ZhuYanzhen1/MM32_CLion/testbench/riccati_solver/riccati_solver.c

#include "riccati_solver.h"
#include "stdio.h"
#include "math.h"

//  P = 96.7181   16.2375   -2.0601
//      16.2375   31.0814    8.2303
//      -2.0601    8.2303   11.3719

#define ITERATION_ACCURACY  0.01f

void solveRiccatiIteration(float A[3][3], float B[3][2], float Q[3][3], float R[2][2]) {
    float matrix_p_next[3][3] = {0}, matrix_p[3][3] = {{Q[0][0], Q[0][1], Q[0][2]},
                                                       {Q[1][0], Q[1][1], Q[1][2]},
                                                       {Q[2][0], Q[2][1], Q[2][2]}};
    for (unsigned int counter = 0; counter < 100000; ++counter) {
        float matrix_at_pn_a[3][3] =
            {{matrix_p[0][0], matrix_p[0][1], A[0][2] * matrix_p[0][0] + A[1][2] * matrix_p[0][1] + matrix_p[0][2]},
             {matrix_p[1][0], matrix_p[1][1], A[0][2] * matrix_p[1][0] + A[1][2] * matrix_p[1][1] + matrix_p[1][2]},
             {A[0][2] * matrix_p[0][0] + A[1][2] * matrix_p[1][0] + matrix_p[2][0],
              A[0][2] * matrix_p[0][1] + A[1][2] * matrix_p[1][1] + matrix_p[2][1],
              A[0][2] * matrix_p[0][2]
                  + A[1][2] * matrix_p[1][2]
                  + A[0][2] * (A[0][2] * matrix_p[0][0] + A[1][2] * matrix_p[1][0] + matrix_p[2][0])
                  + A[1][2] * (A[0][2] * matrix_p[0][1] + A[1][2] * matrix_p[1][1] + matrix_p[2][1]) + matrix_p[2][2]}};
        float
            matrix_at_pn_b[3][2] =
            {{B[0][0] * matrix_p[0][0] + B[1][0] * matrix_p[0][1] + B[2][0] * matrix_p[0][2], B[2][1] * matrix_p[0][2]},
             {B[0][0] * matrix_p[1][0] + B[1][0] * matrix_p[1][1] + B[2][0] * matrix_p[1][2], B[2][1] * matrix_p[1][2]},
             {B[0][0] * (A[0][2] * matrix_p[0][0] + A[1][2] * matrix_p[1][0] + matrix_p[2][0])
                  + B[1][0] * (A[0][2] * matrix_p[0][1] + A[1][2] * matrix_p[1][1] + matrix_p[2][1])
                  + B[2][0] * (A[0][2] * matrix_p[0][2] + A[1][2] * matrix_p[1][2] + matrix_p[2][2]),
              B[2][1] * (A[0][2] * matrix_p[0][2] + A[1][2] * matrix_p[1][2] + matrix_p[2][2])}};
        float matrix_r_bt_pn_b[2][2] =
            {{B[0][0] * (B[0][0] * matrix_p[0][0] + B[1][0] * matrix_p[1][0]
                + B[2][0] * matrix_p[2][0]) + B[1][0] * (B[0][0] * matrix_p[0][1] + B[1][0] * matrix_p[1][1]
                + B[2][0] * matrix_p[2][1])
                  + B[2][0] * (B[0][0] * matrix_p[0][2] + B[1][0] * matrix_p[1][2] + B[2][0] * matrix_p[2][2])
                  + R[0][0],
              B[2][1] * (B[0][0] * matrix_p[0][2] + B[1][0] * matrix_p[1][2] + B[2][0] * matrix_p[2][2])},
             {B[0][0] * B[2][1] * matrix_p[2][0]
                  + B[1][0] * B[2][1] * matrix_p[2][1] + B[2][0] * B[2][1] * matrix_p[2][2],
              B[2][1] * B[2][1] * matrix_p[2][2] + R[0][0]}};
        float
            matrix_bt_pn_a[2][3] =
            {{B[0][0] * matrix_p[0][0] + B[1][0] * matrix_p[1][0]
                  + B[2][0] * matrix_p[2][0],
              B[0][0] * matrix_p[0][1] + B[1][0] * matrix_p[1][1] + B[2][0] * matrix_p[2][1],
              B[0][0] * matrix_p[0][2]
                  + B[1][0] * matrix_p[1][2]
                  + A[0][2] * (B[0][0] * matrix_p[0][0]
                      + B[1][0] * matrix_p[1][0]
                      + B[2][0] * matrix_p[2][0])
                  + A[1][2] * (B[0][0] * matrix_p[0][1]
                      + B[1][0] * matrix_p[1][1] + B[2][0] * matrix_p[2][1]) + B[2][0] * matrix_p[2][2]},
             {B[2][1] * matrix_p[2][0],
              B[2][1] * matrix_p[2][1],
              A[0][2] * B[2][1] * matrix_p[2][0] + A[1][2] * B[2][1] * matrix_p[2][1] + B[2][1] * matrix_p[2][2]}};
        float matrix_inv_r_bt_pn_b[2][2] =
            {{matrix_r_bt_pn_b[1][1]
                  / (-matrix_r_bt_pn_b[0][1] * matrix_r_bt_pn_b[1][0]
                      + matrix_r_bt_pn_b[0][0] * matrix_r_bt_pn_b[1][1]), -(matrix_r_bt_pn_b[0][1]
                / (-matrix_r_bt_pn_b[0][1] * matrix_r_bt_pn_b[1][0]
                    + matrix_r_bt_pn_b[0][0] * matrix_r_bt_pn_b[1][1]))},
             {-(matrix_r_bt_pn_b[1][0]
                 / (-matrix_r_bt_pn_b[0][1] * matrix_r_bt_pn_b[1][0]
                     + matrix_r_bt_pn_b[0][0] * matrix_r_bt_pn_b[1][1])),
              matrix_r_bt_pn_b[0][0] / (-matrix_r_bt_pn_b[0][1] * matrix_r_bt_pn_b[1][0]
                  + matrix_r_bt_pn_b[0][0] * matrix_r_bt_pn_b[1][1])}};
        float another_matrix[3][3] =
            {{(matrix_at_pn_b[0][0] * matrix_inv_r_bt_pn_b[0][0]
                + matrix_at_pn_b[0][1] * matrix_inv_r_bt_pn_b[1][0]) * matrix_bt_pn_a[0][0]
                  + (matrix_at_pn_b[0][0] * matrix_inv_r_bt_pn_b[0][1]
                      + matrix_at_pn_b[0][1] * matrix_inv_r_bt_pn_b[1][1]) * matrix_bt_pn_a[1][0],
              (matrix_at_pn_b[0][0] * matrix_inv_r_bt_pn_b[0][0] +
                  matrix_at_pn_b[0][1] * matrix_inv_r_bt_pn_b[1][0]) * matrix_bt_pn_a[0][1]
                  + (matrix_at_pn_b[0][0] * matrix_inv_r_bt_pn_b[0][1]
                      + matrix_at_pn_b[0][1] * matrix_inv_r_bt_pn_b[1][1]) * matrix_bt_pn_a[1][1],
              (matrix_at_pn_b[0][0] * matrix_inv_r_bt_pn_b[0][0] +
                  matrix_at_pn_b[0][1] * matrix_inv_r_bt_pn_b[1][0]) * matrix_bt_pn_a[0][2]
                  + (matrix_at_pn_b[0][0] * matrix_inv_r_bt_pn_b[0][1]
                      + matrix_at_pn_b[0][1] * matrix_inv_r_bt_pn_b[1][1]) * matrix_bt_pn_a[1][2]},
             {(matrix_at_pn_b[1][0] * matrix_inv_r_bt_pn_b[0][0] +
                 matrix_at_pn_b[1][1] * matrix_inv_r_bt_pn_b[1][0]) * matrix_bt_pn_a[0][0]
                  + (matrix_at_pn_b[1][0] * matrix_inv_r_bt_pn_b[0][1]
                      + matrix_at_pn_b[1][1] * matrix_inv_r_bt_pn_b[1][1]) * matrix_bt_pn_a[1][0],
              (matrix_at_pn_b[1][0] * matrix_inv_r_bt_pn_b[0][0] +
                  matrix_at_pn_b[1][1] * matrix_inv_r_bt_pn_b[1][0]) * matrix_bt_pn_a[0][1]
                  + (matrix_at_pn_b[1][0] * matrix_inv_r_bt_pn_b[0][1]
                      + matrix_at_pn_b[1][1] * matrix_inv_r_bt_pn_b[1][1]) * matrix_bt_pn_a[1][1],
              (matrix_at_pn_b[1][0] * matrix_inv_r_bt_pn_b[0][0] +
                  matrix_at_pn_b[1][1] * matrix_inv_r_bt_pn_b[1][0]) * matrix_bt_pn_a[0][2]
                  + (matrix_at_pn_b[1][0] * matrix_inv_r_bt_pn_b[0][1]
                      + matrix_at_pn_b[1][1] * matrix_inv_r_bt_pn_b[1][1]) * matrix_bt_pn_a[1][2]},
             {(matrix_at_pn_b[2][0] * matrix_inv_r_bt_pn_b[0][0] +
                 matrix_at_pn_b[2][1] * matrix_inv_r_bt_pn_b[1][0]) * matrix_bt_pn_a[0][0]
                  + (matrix_at_pn_b[2][0] * matrix_inv_r_bt_pn_b[0][1]
                      + matrix_at_pn_b[2][1] * matrix_inv_r_bt_pn_b[1][1]) * matrix_bt_pn_a[1][0],
              (matrix_at_pn_b[2][0] * matrix_inv_r_bt_pn_b[0][0] +
                  matrix_at_pn_b[2][1] * matrix_inv_r_bt_pn_b[1][0]) * matrix_bt_pn_a[0][1]
                  + (matrix_at_pn_b[2][0] * matrix_inv_r_bt_pn_b[0][1]
                      + matrix_at_pn_b[2][1] * matrix_inv_r_bt_pn_b[1][1]) * matrix_bt_pn_a[1][1],
              (matrix_at_pn_b[2][0] * matrix_inv_r_bt_pn_b[0][0] +
                  matrix_at_pn_b[2][1] * matrix_inv_r_bt_pn_b[1][0]) * matrix_bt_pn_a[0][2]
                  + (matrix_at_pn_b[2][0] * matrix_inv_r_bt_pn_b[0][1]
                      + matrix_at_pn_b[2][1] * matrix_inv_r_bt_pn_b[1][1]) * matrix_bt_pn_a[1][2]}};
        matrix_p_next[0][0] = matrix_at_pn_a[0][0] - another_matrix[0][0] + Q[0][0];
        matrix_p_next[0][1] = matrix_at_pn_a[0][1] - another_matrix[0][1];
        matrix_p_next[0][2] = matrix_at_pn_a[0][2] - another_matrix[0][2];
        matrix_p_next[1][0] = matrix_at_pn_a[1][0] - another_matrix[1][0];
        matrix_p_next[1][1] = matrix_at_pn_a[1][1] - another_matrix[1][1] + Q[0][0];
        matrix_p_next[1][2] = matrix_at_pn_a[1][2] - another_matrix[1][2];
        matrix_p_next[2][0] = matrix_at_pn_a[2][0] - another_matrix[2][0];
        matrix_p_next[2][1] = matrix_at_pn_a[2][1] - another_matrix[2][1];
        matrix_p_next[2][2] = matrix_at_pn_a[2][2] - another_matrix[2][2] + Q[0][0];

        float p_next_max_coefficient = fabsf(matrix_p_next[0][0]);
        for (unsigned char counter1 = 0; counter1 < 3; ++counter1)
            for (unsigned char counter2 = 0; counter2 < 3; ++counter2)
                if (p_next_max_coefficient < fabsf(matrix_p_next[counter1][counter2]))
                    p_next_max_coefficient = fabsf(matrix_p_next[counter1][counter2]);

        float p_max_coefficient = fabsf(matrix_p[0][0]);
        for (unsigned char counter1 = 0; counter1 < 3; ++counter1)
            for (unsigned char counter2 = 0; counter2 < 3; ++counter2)
                if (p_max_coefficient < fabsf(matrix_p[counter1][counter2]))
                    p_max_coefficient = fabsf(matrix_p[counter1][counter2]);

        if (fabsf(p_max_coefficient - p_next_max_coefficient) < ITERATION_ACCURACY) {
            printf("\r\niteration counter:%d\r\n", counter);
            break;
        }

        for (unsigned char counter1 = 0; counter1 < 3; ++counter1)
            for (unsigned char counter2 = 0; counter2 < 3; ++counter2)
                matrix_p[counter1][counter2] = matrix_p_next[counter1][counter2];
    }

    printf("------------Matrix P------------\r\n");
    for (int counter1 = 0; counter1 < 3; ++counter1) {
        for (int counter2 = 0; counter2 < 3; ++counter2)
            printf("%f   ", matrix_p[counter1][counter2]);
        printf("\r\n");
    }
}
