ZhuYanzhen1/MM32_CLion/program/math/path.c

/**************************************************************************/ /**
    \file     path.c
    \brief    Contains track points
    \author   ZGL
    \version  V1.6.1
    \date     24. July 2022
 ******************************************************************************/

#include "path.h"

float test_point[][4] = {
    {4302.6909513f, 39718.6588341f, 3.0595232f, 0.0002376f},
    {4302.2433562f, 39718.6956507f, 3.0787849f, 0.0009164f},
    {4301.7594206f, 39718.7260856f, 3.0838215f, 0.0003204f},
    {4301.2719785f, 39718.7542770f, 3.0873939f, 0.0001274f},
    {4300.7692807f, 39718.7815493f, 3.0928840f, 0.0002585f},
    {4300.2493526f, 39718.8068944f, 3.0954987f, 0.0001789f},
    {4299.7288173f, 39718.8309050f, 3.1034684f, 0.0004699f},
    {4299.1937356f, 39718.8513145f, 3.1115700f, 0.0005022f},
    {4298.6453620f, 39718.8677830f, 3.1129434f, 0.0001222f},
    {4298.1037258f, 39718.8833047f, 3.1148885f, 0.0001497f},
    {4297.5657533f, 39718.8976742f, 3.0111398f, 0.0072814f},
    {4297.0174779f, 39718.9696068f, 2.9971062f, 0.0009579f},
    {4296.4701301f, 39719.0492461f, 3.0061274f, 0.0004470f},
    {4295.9127171f, 39719.1252215f, 3.0175074f, 0.0005869f},
    {4295.3428454f, 39719.1962994f, 3.0307719f, 0.0009550f},
    {4294.7751609f, 39719.2594694f, 3.0416822f, 0.0006085f},
    {4294.1960448f, 39719.3175225f, 3.0546844f, 0.0008802f},
    {4293.6147403f, 39719.3681702f, 3.0611917f, 0.0002613f},
    {4293.0142663f, 39719.4165532f, 3.0723577f, 0.0008467f},
    {4292.4209396f, 39719.4576979f, 3.0783939f, 0.0003856f},
    {4291.8231457f, 39719.4955281f, 3.0847742f, 0.0003889f},
    {4291.2175311f, 39719.5299753f, 3.0919340f, 0.0005399f},
    {4290.6178780f, 39719.5597778f, 3.0953611f, 0.0001098f},
    {4289.9948902f, 39719.5886000f, 3.0998538f, 0.0004809f},
    {4289.4025012f, 39719.6133400f, 3.1031333f, 0.0001459f},
    {4288.7926511f, 39719.6368060f, 3.1079789f, 0.0003114f},
    {4288.1764860f, 39719.6575254f, 3.1112980f, 0.0002353f},
    {4287.5611374f, 39719.6761729f, 3.1130251f, 0.0001703f},
    {4286.9598236f, 39719.6933556f, 3.1154136f, 0.0002034f},
    {4286.3692413f, 39719.7088200f, 3.1162437f, 0.0000527f},
    {4285.7769171f, 39719.7238380f, 3.1182080f, 0.0001295f},
    {4285.1819254f, 39719.7377542f, 3.1203890f, 0.0001648f},
    {4284.5913329f, 39719.7502788f, 3.1226512f, 0.0001473f},
    {4283.9962996f, 39719.7615509f, 3.1255383f, 0.0002317f},
    {4283.4142696f, 39719.7708958f, 3.1252645f, 0.0000316f},
    {4282.8257427f, 39719.7805062f, 3.1284448f, 0.0002064f},
    {4282.2287684f, 39719.7883556f, 3.1298461f, 0.0000913f},
    {4281.6273916f, 39719.7954201f, 3.1329040f, 0.0002089f},
    {4281.0222524f, 39719.8006780f, 3.1305565f, 0.0001601f},
    {4280.4213272f, 39719.8073102f, 3.1324097f, 0.0001227f},
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
};
