ZhuYanzhen1/MM32_CLion/program/math/data_conversion.c

/**************************************************************************/ /**
    \file       data_conversion.c
    \brief      Coordinate system transformation
                Data Transformation
    \author     ZGL
    \version    V1.6.1
    \date       24. July 2022
******************************************************************************/

#include "data_conversion.h"
#include "qfplib.h"
#include "gps_parser.h"
#include "sensor_decode.h"
#include "fast_math.h"
#include "kalman.h"

extern kalman_data_t kalman_data;

/*! \brief Status information in the neu coordinates */
neu_infomation neu = {0};

/*!
    \brief      Get the distance based on the latitude and longitude of the starting point
                and the latitude and longitude of the current state
    \param[in]  lat_1(°):Starting latitude
    \param[in]  lon_1(°):Starting longitude
    \param[in]  lat_2(°):Latitude of Present State
    \param[in]  lon_2(°):longitude of Present State
    \retval     Distance between two points on the earth
    \note       When we keep the longitude the same, we can calculate the distance to the north
                When we keep the latitude the same, we can calculate the distance to the east
*/
float get_distance(float lat_2, float lon_2, float lat_1, float lon_1) {
    float temp =
        my_pow(qfp_fsin(GEO_ANGLE((lat_1 - lat_2) * 0.5f)), 2) +
            qfp_fcos(GEO_ANGLE(lat_1)) * qfp_fcos(GEO_ANGLE(lat_2))
                * my_pow(qfp_fsin(GEO_ANGLE((lon_1 - lon_2) * 0.5f)), 2);
    float distance = 2 * EARTH_RADIUS * my_asin(qfp_fsqrt(temp));
    return distance;
}

/*!
    \brief      Convert latitude to displacement in ENU coordinate system
    \param[in]  latitude(°)
    \retval     Converted data
*/
float get_distance_m_lat(float lat) {
    float distance = GEO_ANGLE(lat);
    return EARTH_RADIUS * distance;
}

/*!
    \brief      Convert longitude to displacement in ENU coordinate system
    \param[in]  longitude(°)
    \retval     Converted data
*/
float get_distance_m_lon(float lon) {
    float distance = GEO_ANGLE(lon);
    return EARTH_RADIUS * distance;
}

/*!
    \brief  Converting GPS-derived latitude,
            longitude, velocity and acceleration into the international system of units
*/
void sensor_unit_conversion() {
    if (small_packets_sum.num == 0)
        small_packets_sum.ay = 0;
    else
        small_packets_sum.ay /= (float) small_packets_sum.num;
    neu.acceleration = MG_TO_M_S_2(small_packets_sum.ay * FACTOR_ALLC_Y);   // 车头前进的方向时y的正方向
    small_packets_sum.num = 0;
    small_packets_sum.ay = 0;

    float temp_v = (float) gps_rmc.speed_to_ground_section;
    int v_decimal = num_times_nth_power_of_10(1, gps_rmc.decimal_places_speed);
    neu.v = KNOT_TO_M_S(temp_v / v_decimal);
}

/*
    \brief  The velocity obtained after Kalman filtering
            becomes the velocity in the northeast sky coordinate system
*/
void coordinate_system_transformation_kalman_v(float delta) {
    float temp_delta = GEO_ANGLE(delta);
    neu.north_v = kalman_data.v * qfp_fcos(temp_delta);
    neu.east_v = kalman_data.v * qfp_fsin(temp_delta);
}
