ZhuYanzhen1/MM32_CLion/program/math/path.h

/**************************************************************************/ /**
    \file     path.h
    \brief    Contains macros related to track points
    \author   ZGL
    \version  V1.6.1
    \date     24. July 2022
 ******************************************************************************/

#ifndef MM32F3277_MATH_TEST_H_
#define MM32F3277_MATH_TEST_H_

/*! \brief Number of track points */
#define INDEX_NUM   700

extern float test_point[][4];

#endif // MM32F3277_MATH_TEST_H_
