ZhuYanzhen1/MM32_CLion/program/hardware/gpio.c

/**************************************************************************/ /**
    \file       gpio.c
    \brief      GPIO function Source File
    \author     LaoZhu
    \version    V1.6.1
    \date       24. July 2022
******************************************************************************/

#include "gpio.h"
#ifdef IS_CONTROL_MCU
#include "../ctrl_mcu/config.h"
#include "../ctrl_mcu/pin.h"
#else
#include "../proc_mcu/config.h"
#include "../proc_mcu/pin.h"
#endif  // IS_CONTROL_MCU
#include "hal_conf.h"
#include "mm32_device.h"

#ifdef IS_CONTROL_MCU

void tim3_pwm_gpio_config(void) {
    GPIO_InitTypeDef GPIO_InitStructure;
    RCC_AHBPeriphClockCmd(RCC_AHBPeriph_GPIOB, ENABLE);
    GPIO_InitStructure.GPIO_Pin = GPIO_Pin_4;
    GPIO_InitStructure.GPIO_Mode = GPIO_Mode_Out_PP;
    GPIO_InitStructure.GPIO_Speed = GPIO_Speed_50MHz;
    GPIO_Init(GPIOB, &GPIO_InitStructure);
    GPIO_ResetBits(GPIOB, GPIO_Pin_4);
}

#endif
#ifdef IS_PROCESS_MCU
void lcd_gpio_config(void) {
    GPIO_InitTypeDef GPIO_InitStruct;
    RCC_AHBPeriphClockCmd(RCC_AHBENR_GPIOE, ENABLE);

    GPIO_StructInit(&GPIO_InitStruct);
    GPIO_InitStruct.GPIO_Pin = LCD_A0_PIN;
    GPIO_InitStruct.GPIO_Speed = GPIO_Speed_50MHz;
    GPIO_InitStruct.GPIO_Mode = GPIO_Mode_Out_PP;
    GPIO_Init(LCD_A0_PORT, &GPIO_InitStruct);

    GPIO_StructInit(&GPIO_InitStruct);
    GPIO_InitStruct.GPIO_Pin = LCD_RES_PIN;
    GPIO_InitStruct.GPIO_Speed = GPIO_Speed_50MHz;
    GPIO_InitStruct.GPIO_Mode = GPIO_Mode_Out_PP;
    GPIO_Init(LCD_RES_PORT, &GPIO_InitStruct);
}

void xpt2046_gpio_config(void) {
    GPIO_InitTypeDef GPIO_InitStruct;
    NVIC_InitTypeDef NVIC_InitStruct;
    EXTI_InitTypeDef EXTI_InitStruct;

    RCC_APB2PeriphClockCmd(RCC_APB2ENR_SYSCFG, ENABLE);
    RCC_AHBPeriphClockCmd(RCC_AHBENR_GPIOE, ENABLE);

    GPIO_StructInit(&GPIO_InitStruct);
    GPIO_InitStruct.GPIO_Pin = TOUCH_CS_PIN;
    GPIO_InitStruct.GPIO_Speed = GPIO_Speed_50MHz;
    GPIO_InitStruct.GPIO_Mode = GPIO_Mode_Out_PP;
    GPIO_Init(TOUCH_CS_PORT, &GPIO_InitStruct);

    GPIO_StructInit(&GPIO_InitStruct);
    GPIO_InitStruct.GPIO_Pin = TOUCH_PEN_PIN;
    GPIO_InitStruct.GPIO_Speed = GPIO_Speed_50MHz;
    GPIO_InitStruct.GPIO_Mode = GPIO_Mode_IPU;
    GPIO_Init(TOUCH_PEN_PORT, &GPIO_InitStruct);

    SYSCFG_EXTILineConfig(EXTI_PortSourceGPIOE, EXTI_PinSource4);
    EXTI_InitStruct.EXTI_Line = EXTI_Line4;
    EXTI_InitStruct.EXTI_Mode = EXTI_Mode_Interrupt;
    EXTI_InitStruct.EXTI_Trigger = EXTI_Trigger_Falling;
    EXTI_InitStruct.EXTI_LineCmd = ENABLE;
    EXTI_Init(&EXTI_InitStruct);

    NVIC_InitStruct.NVIC_IRQChannel = EXTI4_IRQn;
    NVIC_InitStruct.NVIC_IRQChannelPreemptionPriority = EXTI4_PRIORITY;
    NVIC_InitStruct.NVIC_IRQChannelSubPriority = 0;
    NVIC_InitStruct.NVIC_IRQChannelCmd = ENABLE;
    NVIC_Init(&NVIC_InitStruct);

    GPIO_SetBits(TOUCH_PEN_PORT, TOUCH_PEN_PIN);
    GPIO_SetBits(TOUCH_CS_PORT, TOUCH_CS_PIN);
}
#endif  // IS_PROCESS_MCU
