ZhuYanzhen1/MM32_CLion/program/hardware/timer.h

/**************************************************************************/ /**
    \file     timer.h
    \brief    Tim function Header File
    \author   Lao·Zhu
    \version  V1.6.1
    \date     24. July 2022
******************************************************************************/

#ifndef MM32F3277_HARDWARE_TIMER_H_
#define MM32F3277_HARDWARE_TIMER_H_

void timer2_config();
void timer3_config(void);

#endif // MM32F3277_HARDWARE_TIMER_H_
