ZhuYanzhen1/MM32_CLion/program/math/kalman.h

/**************************************************************************/ /**
    \file       kalman.h
    \brief      Kalman Fusion Header File
    \author     ZGL
    \version    V1.6.1
    \date       24. July 2022
******************************************************************************/

#ifndef MM32F3277_MATH_KALMAN_H_
#define MM32F3277_MATH_KALMAN_H_

#define V_Q_POS     0.2f
#define DIS_Q_POS   0.8f

/*! \brief The data after performing Kalman fusion */
typedef struct {
    float v;
    float distance_north;
    float distance_east;
} kalman_data_t;

typedef struct {
    float q_pos; // Process noise variance for the position
    float q_vel; // Process noise variance for the velocity
    float r_pos; // Measurement noise variance - this is actually the variance of the measurement noise
    float r_old_pos;

    float pos;   // The pos calculated by the Kalman filter - part of the 2x1 state vector
    float vel;   // The gyro velocity calculated by the Kalman filter - part of the 2x1 state vector
    float bias;  // The bias of velocity

    float P[2][2]; // Error covariance 2x2 matrix
    unsigned char gps_valid_flag;
} kalman_filter_t;

void kalman_config_angle(kalman_filter_t *kalman, float pos_0);
void kalman_config_v(kalman_filter_t *kalman);
void kalman_config_distance(kalman_filter_t *kalman, float pos_0);
float kalman_update(kalman_filter_t *kalman, float new_pos, float new_vel, float dt);
void kalman_config();

#endif //MM32F3277_MATH_KALMAN_H_
