ZhuYanzhen1/MM32_CLion/program/math/filter.h

/**************************************************************************/ /**
    \file       filter.H
    \brief      Includes some filtering algorithms
    \author     Lao·Zhu & ZGL
    \version    V1.6.1
    \date       24. July 2022
******************************************************************************/

#ifndef MM32F3277_MATH_FILTER_H_
#define MM32F3277_MATH_FILTER_H_

typedef struct {
    unsigned char m;
    float ep;
    float A[2];
    float d1[2];
    float d2[2];
    float w0[2];
    float w1[2];
    float w2[2];
} CHELowPass;

void create_che_low_pass_filter(float epsilon, float sampling_frequency,
                                float half_power_frequency, CHELowPass *filter);

float che_low_pass(CHELowPass *filter, float input);
float rc_low_pass(float input, float last_output, float a);

#endif // MM32F3277_MATH_FILTER_H_
