ZhuYanzhen1/MM32_CLion/program/math/sort.h

/**************************************************************************/ /**
    \file     sort.h
    \brief    sort function Header File
    \author   Lao·Zhu
    \version  V1.6.1
    \date     24. July 2022
 ******************************************************************************/

#ifndef MM32F3277_MATH_SORT_H_
#define MM32F3277_MATH_SORT_H_

void sort_heapsort(int *a, int len);
void sort_mergesort(int *a, int len);
void sort_quicksort(int *a, int len);

#endif // MM32F3277_MATH_SORT_H_
