ZhuYanzhen1/MM32_CLion/program/hardware/led.c

/**************************************************************************/ /**
    \file     led.c
    \brief    LED function Source File
    \author   Lao·Zhu
    \version  V1.6.1
    \date     24. July 2022
 ******************************************************************************/

#include "led.h"
#include "hal_conf.h"
#include "mm32_device.h"
#ifdef IS_CONTROL_MCU
#include "../ctrl_mcu/pin.h"
#else
#include "../proc_mcu/pin.h"
#endif // IS_CONTROL_MCU

void led_config(void) {
    GPIO_InitTypeDef GPIO_InitStruct;
    RCC_AHBPeriphClockCmd(RCC_AHBENR_GPIOA, ENABLE);

    GPIO_StructInit(&GPIO_InitStruct);
    GPIO_InitStruct.GPIO_Pin = LED1_PIN;
    GPIO_InitStruct.GPIO_Speed = GPIO_Speed_50MHz;
    GPIO_InitStruct.GPIO_Mode = GPIO_Mode_Out_PP;
    GPIO_Init(LED1_PORT, &GPIO_InitStruct);

    LED1_OFF();
}
