ZhuYanzhen1/MM32_CLion/testbench/script/sensor_decode_test.h

//
// Created by 16625 on 2022-03-09.
//

#ifndef TESTBENCH_SENSOR_DECODE_TEST_H
#define TESTBENCH_SENSOR_DECODE_TEST_H

void test_nmea_gnrmc_analysis();

void test_precossing_proc_to_control();

#endif //TESTBENCH_SENSOR_DECODE_TEST_H
