ZhuYanzhen1/MM32_CLion/testbench/script/test_data.c

//
// Created by 16625 on 2022-05-03.
//

#include "test_data.h"

float test_point_1[INDEX_NUM + 1][4] = {
        {4385.7630000f, 39692.2030000f, -1.3563084f, 0.0000941f},
        {4385.7795000f, 39692.1272000f, -1.2887732f, 0.0000941f},
        {4385.8010500f, 39692.0527800f, -1.2309500f, 0.0038835f},
        {4385.8403450f, 39691.9416020f, -1.2925674f, 0.0011230f},
        {4385.8787105f, 39691.8072418f, -1.3911715f, 0.0010637f},
        {4385.9136395f, 39691.6148176f, -1.3001896f, 0.0002360f},
        {4385.9695755f, 39691.4131359f, -1.2997348f, 0.0008826f},
        {4386.0353180f, 39691.1765223f, -1.3018036f, 0.0011004f},
        {4386.1146862f, 39690.8885700f, -1.2569980f, 0.0000745f},
        {4386.2070175f, 39690.6040130f, -1.2850957f, 0.0005151f},
        {4386.2984158f, 39690.2928117f, -1.3026813f, 0.0007120f},
        {4386.3961742f, 39689.9369306f, -1.2838052f, 0.0000700f},
        {4386.5025568f, 39689.5764375f, -1.2755703f, 0.0001212f},
        {4386.6145011f, 39689.2082938f, -1.2969585f, 0.0002009f},
        {4386.7220510f, 39688.8253644f, -1.3156845f, 0.0001135f},
        {4386.8192459f, 39688.4526279f, -1.3600625f, 0.0003184f},
        {4386.9071213f, 39688.0417651f, -1.3480107f, 0.0001613f},
        {4387.0046092f, 39687.6113886f, -1.3212981f, 0.0001997f},
        {4387.1088483f, 39687.2022498f, -1.3448423f, 0.0002882f},
        {4387.2105634f, 39686.7597248f, -1.3413798f, 0.0001215f},
        {4387.3174071f, 39686.3021523f, -1.3396726f, 0.0001850f},
        {4387.4193664f, 39685.8688371f, -1.3390615f, 0.0002534f},
        {4387.5286297f, 39685.4057534f, -1.3638710f, 0.0001251f},
        {4387.6299668f, 39684.9229780f, -1.3387958f, 0.0002250f},
        {4387.7366701f, 39684.4712802f, -1.3635255f, 0.0001994f},
        {4387.8380031f, 39683.9893522f, -1.3582755f, 0.0001804f},
        {4387.9480028f, 39683.4795170f, -1.3569844f, 0.0002608f},
        {4388.0489025f, 39683.0147653f, -1.3894093f, 0.0001370f},
        {4388.1392122f, 39682.5222888f, -1.4130893f, 0.0000703f},
        {4388.2206910f, 39682.0098599f, -1.4175950f, 0.0001171f},
        {4388.2938219f, 39681.5361739f, -1.4416880f, 0.0000717f},
        {4388.3590397f, 39681.0337565f, -1.4583259f, 0.0000308f},
        {4388.4177358f, 39680.5139809f, -1.4758974f, 0.0000332f},
        {4388.4697622f, 39679.9672828f, -1.4835378f, 0.0000119f},
        {4388.5164860f, 39679.4330545f, -1.4900661f, 0.0000058f},
        {4388.5591374f, 39678.9057490f, -1.5007573f, 0.0000113f},
        {4388.5973236f, 39678.3612741f, -1.5035798f, 0.0000157f},
        {4388.6320913f, 39677.8446467f, -1.5119667f, 0.0000038f},
        {4388.6629821f, 39677.3199821f, -1.5223776f, 0.0000078f},
        {4388.6895839f, 39676.7707838f, -1.5414582f, 0.0000002f},
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
};
