ZhuYanzhen1/MM32_CLion/program/form/calibrate_form/calibrate_mag_form.h

/**************************************************************************/ /**
    \file       calibrate_mag_form.h
    \brief      calibrate_mag_form function Header File
    \author     LaoZhu
    \version    V1.6.1
    \date       24. July 2022
******************************************************************************/

#ifndef MM32F3277_FORM_MAG_CALIBRATE_FROM_H_
#define MM32F3277_FORM_MAG_CALIBRATE_FROM_H_

void gui_mag_calibrate_form_init();

#endif // MM32F3277_FORM_MAG_CALIBRATE_FROM_H_
