ZhuYanzhen1/MM32_CLion/program/form/calibrate_form/calibrate_touch_form.h

/**************************************************************************/ /**
    \file       calibrate_touch_form.h
    \brief      calibrate_touch_form function Header File
    \author     LaoZhu
    \version    V1.6.1
    \date       24. July 2022
******************************************************************************/

#ifndef MM32F3277_FORM_CALIBRATE_FORM_CALIBRATE_TOUCH_FORM_H_
#define MM32F3277_FORM_CALIBRATE_FORM_CALIBRATE_TOUCH_FORM_H_

void gui_calibrate_touch_form_init(void);

#endif // MM32F3277_FORM_CALIBRATE_FORM_CALIBRATE_TOUCH_FORM_H_
