ZhuYanzhen1/MM32_CLion/testbench/script/solver_test.h

//
// Created by Lao·Zhu on 2022/2/3.
//

#ifndef TESTBENCH_SCRIPT_SOLVER_TEST_H_
#define TESTBENCH_SCRIPT_SOLVER_TEST_H_

void test_calibration_solver(void);

void test_riccati_solver(void);

void test_project_solver(void);

#endif //TESTBENCH_SCRIPT_SOLVER_TEST_H_
