ZhuYanzhen1/MM32_CLion/testbench/script/test_data.h

//
// Created by 16625 on 2022-03-30.
//

#ifndef TESTBENCH_TEST_DATA_H
#define TESTBENCH_TEST_DATA_H

#define INDEX_NUM       747

extern float test_point_1[INDEX_NUM + 1][4];

#endif  // TESTBENCH_TEST_DATA_H
