ZhuYanzhen1/MM32_CLion/testbench/script/verification_test.h

//
// Created by LaoZhu on 2022/3/9.
//

#ifndef TESTBENCH_VERIFICATION_TEST_H
#define TESTBENCH_VERIFICATION_TEST_H

void test_verification_checksum(void);

void test_verification_checkxor(void);

void test_verification_crc8(void);

void test_verification_crc16(void);

#endif //TESTBENCH_VERIFICATION_TEST_H
