ZhuYanzhen1/MM32_CLion/testbench/script/operations_test.h

//
// Created by Lao·Zhu on 2021/12/9.
//

#ifndef TESTBENCH__OPERATIONS_TEST_H_
#define TESTBENCH__OPERATIONS_TEST_H_

void test_operation_arctan(void);

void test_operation_sqrt(void);

#endif //TESTBENCH__OPERATIONS_TEST_H_
