ZhuYanzhen1/MM32_CLion/testbench/script/sort_test.h

//
// Created by Lao·Zhu on 2021/12/25.
//

#ifndef TESTBENCH_SCRIPT_SORT_TEST_H_
#define TESTBENCH_SCRIPT_SORT_TEST_H_

void test_heap_sort(void);
void test_quick_sort(void);
void test_merge_sort(void);

#endif //TESTBENCH_SCRIPT_SORT_TEST_H_
