ZhuYanzhen1/MM32_CLion/testbench/script/gps_text.c

//
// Created by 16625 on 2021-12-23.
//

#include "gps_text.h"
#include "CUnit/Basic.h"
#include "gps_praser.h"
#include "malloc.h"

void test_nmea_comma_position() {
    char data[] = "$GPGGA,235316.000,3959.9925,S,12000.0090,E,1,06,1.21,62.77,M,0.00,M,,*7B";
    char *p = data;
    int n1 = nmea_comma_position(data, 2);
    CU_ASSERT_EQUAL(*(p + n1), '3');
    CU_ASSERT_NOT_EQUAL(*(p + n1), 'J');
    CU_ASSERT_EQUAL(n1, 18);
    CU_ASSERT_NOT_EQUAL(n1, 17);
    int n2 = nmea_comma_position(data, 3);
    CU_ASSERT_EQUAL(*(p + n2), 'S');
    CU_ASSERT_NOT_EQUAL(*(p + n2), '0');
    CU_ASSERT_EQUAL(n2, 28);
    CU_ASSERT_EQUAL(n2 - n1, 10);
    CU_ASSERT_NOT_EQUAL(n2, 29);
    int n3 = nmea_comma_position(data, 20);
    CU_ASSERT_NOT_EQUAL(*(p + n3), '0');
    CU_ASSERT_EQUAL(n3, 0XFF); //FAULT
    CU_ASSERT_NOT_EQUAL(n3, sizeof(data));
}

void text_nmea_pow() {
    CU_ASSERT_EQUAL(nmea_pow(10, 2), 100);
    CU_ASSERT_NOT_EQUAL(nmea_pow(10, 8), 100);
    CU_ASSERT_EQUAL(nmea_pow(10, 0), 1);
    CU_ASSERT_NOT_EQUAL(nmea_pow(10, 0), 10);
    CU_ASSERT_NOT_EQUAL(nmea_pow(10, 8), 1);
}

void test_nmea_str2num() {
    char *data[] = {"3424,", "-234,", "34.32,", "-23.43,", "0.661,"};
    char **p = data;
    CU_ASSERT_EQUAL(nmea_str2num(data[0]), 3424);
    CU_ASSERT_EQUAL(nmea_str2num(p[1]), -234);
//    CU_ASSERT_EQUAL(nmea_str2num(p[2]), 34.32);   //TRUE
//    CU_ASSERT_EQUAL(nmea_str2num(p[3]), -23.43);  //TRUE
//    CU_ASSERT_EQUAL(nmea_str2num(p[4]), 0.661);   //TRUE
    CU_ASSERT_NOT_EQUAL(nmea_str2num(p[0]), 13424);
    CU_ASSERT_NOT_EQUAL(nmea_str2num(p[1]), -13424);
    CU_ASSERT_NOT_EQUAL(nmea_str2num(p[2]), 13.424);
    CU_ASSERT_NOT_EQUAL(nmea_str2num(p[3]), -13.424);
    CU_ASSERT_NOT_EQUAL(nmea_str2num(p[4]), 0.134);


}

void text_nmea_gpgga_analysis() {
    char data[] = "$GPGGA,235316.000,3959.9925,S,12000.0090,E,1,06,1.21,62.77,M,0.00,M,,*7B";
    nmea_gga *gpsx = malloc(sizeof(*gpsx));
    nmea_gpgga_analysis(gpsx, data);
    CU_ASSERT_EQUAL(gpsx->latitude_direction, 'S');
    CU_ASSERT_EQUAL(gpsx->checksum, 0X7B);
    CU_ASSERT_EQUAL(gpsx->height_unit_altitude, 'M');
}
